congiants/Temperature_Predictor/firmware/esp8266/secrets.example.h

// Template for secrets.h. Copy this file to secrets.h in the same folder
// and fill in your own values. secrets.h is gitignored: never commit it.
#define WIFI_SSID     "your-2.4GHz-wifi-name"
#define WIFI_PASSWORD "your-wifi-password"
#define API_URL       "http://<pc-lan-ip>:8000/readings"
#define DEVICE_ID     "<device_id returned by POST /devices>"
#define DEVICE_TOKEN  "<token returned by POST /devices (shown once)>"
